stephentissot/NodeNet-SoC-Risc-v/README_NODENET_PLC_COMMANDS.md

# NodeNet PLC Commands

This document describes the NodeNet PLC commands implemented by the firmware for browsing point definitions, browsing point states, managing PLC slots, and deploying PLC programs.

These commands are handled in the NodeNet core and operate on the local point catalog.

Current status: the project is **PLC Ready** with a **V0 basic ISA**. The canonical deployment artifact is a relocatable `objectFileV1` payload uploaded over NodeNet and linked by firmware against the current runtime point catalog.

## Overview

Supported commands:

- `pointDefsReq`
- `pointStatesReq`
- `pointUpsert`
- `pointDelete`
- `plcStatusReq`
- `plcSlotsReq`
- `plcLoadReq`
- `plcBytecodeReq`
- `plcUploadBeginReq`
- `plcUploadStatusReq`
- `plcUploadCommitReq`
- `plcUploadAbortReq`
- `updateProperty` for writable local properties and writable Modbus coil points

PLC upload persistence rules:

- uploads are staged in SDRAM and currently require `autoLoad = true`
- `persistToFlash = true` stores the current slot set in the raw PLC flash package for reboot restore
- `persistToFlash = false` keeps the uploaded artifact volatile

The point identity model is hierarchical:

- `deviceId`
- `feature`
- `pointId`

The optional `path` field used by `pointDefsReq` and `pointStatesReq` is built like this:

```text
deviceId.feature.pointId
```

Examples:

- empty path: browse devices
- `gb9fao5yk4f`: browse one device and its features
- `gb9fao5yk4f.modbus0.eurotherm6100`: browse points under one feature
- `gb9fao5yk4f.modbus0.eurotherm6100.ch1`: browse one exact point

Both browse commands support pagination:

- `offset`: first element to return
- `limit`: maximum number of elements to return
- `count`: number of elements returned in this response
- `total`: total number of matching elements
- `hasMore`: `true` when more elements are available

Transport note:

- when requests are sent from a PC through the NodeNet master bridge, use `from = 255`
- the firmware routes replies back to `request.from`
- `from = 255` is treated as the desktop endpoint and the reply is re-emitted so the PC can receive it through the master
- using `from = 5` or another regular NodeNet address sends the reply to that NodeNet node, not back to the PC link

## plcBytecodeReq

Reads back the linked PLC bytecode currently loaded in one slot.

This command returns the runtime-linked bytecode stored in the slot SDRAM region,
not the original `objectFileV1` source artifact. Symbolic point names are therefore
not preserved in the returned bytes.

### Request

```json
{
  "cmd": "plcBytecodeReq",
  "from": 255,
  "to": 4,
  "slotId": 0,
  "offset": 0,
  "maxBytes": 768
}
```

Fields:

- `slotId`: slot to inspect
- `offset`: byte offset inside the linked slot bytecode
- `maxBytes`: requested maximum chunk size, capped by firmware

### Success response

```json
{
  "cmd": "plcBytecodeRes",
  "ok": true,
  "slotId": 0,
  "offset": 0,
  "count": 96,
  "totalSize": 96,
  "hasMore": false,
  "encoding": "base64",
  "dataBase64": "ECoAEQEA"
}
```

Fields:

- `count`: number of decoded bytecode bytes in this chunk
- `totalSize`: total linked bytecode size for the slot
- `hasMore`: `true` when another chunk must be requested
- `dataBase64`: Base64-encoded linked bytecode bytes

### Failure responses

Possible firmware error values:

- `slotOutOfRange`
- `slotNotLoaded`
- `offsetOutOfRange`

## plcObjectFileReq

Reads back the original `objectFileV1` payload currently retained for one slot.

This command returns the per-slot source artifact snapshot kept in SDRAM after a
successful load. Symbol names, `PARAM`, and `VAR` declarations are preserved and
can be reconstructed by the desktop disassembler.

Persistence note:

- slot `0` can retain a reboot-persistent PLC package in flash
- other slots retain their source snapshot only while the current runtime stays loaded

### Request

```json
{
  "cmd": "plcObjectFileReq",
  "from": 255,
  "to": 4,
  "slotId": 0,
  "offset": 0,
  "maxBytes": 768
}
```

Fields:

- `slotId`: slot to inspect
- `offset`: byte offset inside the retained `objectFileV1` payload
- `maxBytes`: requested maximum chunk size, capped by firmware

### Success response

```json
{
  "cmd": "plcObjectFileRes",
  "ok": true,
  "slotId": 0,
  "offset": 0,
  "count": 164,
  "totalSize": 164,
  "payloadCrc32": 305419896,
  "artifactType": "objectFileV1",
  "hasMore": false,
  "encoding": "base64",
  "dataBase64": "..."
}
```

Fields:

- `count`: number of decoded object bytes in this chunk
- `totalSize`: total retained object size for the slot
- `payloadCrc32`: checksum of the retained object payload
- `artifactType`: always `objectFileV1`
- `hasMore`: `true` when another chunk must be requested
- `dataBase64`: Base64-encoded object bytes

### Failure responses

Possible firmware error values:

- `slotOutOfRange`
- `objectFileUnavailable`
- `encodingFailed`

## pointDefsReq

Requests point definitions from the local catalog.

### Request

```json
{
  "cmd": "pointDefsReq",
  "from": 5,
  "to": 4,
  "path": "",
  "offset": 0,
  "limit": 8
}
```

### Device-level response

With an empty path, or with a `deviceId`, the response kind is `devices`.

```json
{
  "cmd": "pointDefsRes",
  "to": 5,
  "path": "",
  "offset": 0,
  "kind": "devices",
  "count": 1,
  "total": 1,
  "hasMore": false,
  "devices": [
    {
      "deviceId": "gb9fao5yk4f",
      "features": [
        "core",
        "modbus0",
        "modbus0.waveshare8ch",
        "modbus0.eurotherm6100"
      ]
    }
  ]
}
```

### Feature-level response

With a `deviceId.feature` path, the response kind is `points`.

```json
{
  "cmd": "pointDefsRes",
  "to": 5,
  "path": "gb9fao5yk4f.modbus0.eurotherm6100",
  "offset": 0,
  "kind": "points",
  "count": 3,
  "total": 3,
  "hasMore": false,
  "points": [
    {
      "deviceId": "gb9fao5yk4f",
      "feature": "modbus0.eurotherm6100",
      "pointId": "ch1",
      "displayName": "Eurotherm CH1 PV",
      "backend": 1,
      "direction": 0,
      "valueType": 2,
      "refreshMs": 1000,
      "timeoutMs": 3000,
      "stringCapacity": 0,
      "portIndex": 0,
      "slaveAddress": 2,
      "address": 41433,
      "registerCount": 1,
      "table": 3,
      "access": 1
    }
  ]
}
```

## pointStatesReq

Requests live point states from the local catalog.

### Request

```json
{
  "cmd": "pointStatesReq",
  "from": 5,
  "to": 4,
  "path": "gb9fao5yk4f.modbus0.eurotherm6100",
  "offset": 0,
  "limit": 4
}
```

### Point-state response

With a `deviceId.feature` or `deviceId.feature.pointId` path, the response kind is `points` and the returned array is `pointStates`.

`lastUpdateAgeMs` is the elapsed time in milliseconds since the last poll or write attempt for that point.

`lastGoodUpdateAgeMs` is the elapsed time in milliseconds since the last successful poll or write for that point. It stays `0` if the point has never had a good value yet.

```json
{
  "cmd": "pointStatesRes",
  "to": 5,
  "path": "gb9fao5yk4f.modbus0.eurotherm6100",
  "offset": 0,
  "kind": "points",
  "count": 3,
  "total": 3,
  "hasMore": false,
  "pointStates": [
    {
      "deviceId": "gb9fao5yk4f",
      "feature": "modbus0.eurotherm6100",
      "pointId": "ch1",
      "quality": 1,
      "lastUpdateAgeMs": 183,
      "lastGoodUpdateAgeMs": 183,
      "value": 215
    },
    {
      "deviceId": "gb9fao5yk4f",
      "feature": "modbus0.eurotherm6100",
      "pointId": "ch2",
      "quality": 1,
      "lastUpdateAgeMs": 1186,
      "lastGoodUpdateAgeMs": 1186,
      "value": 198
    }
  ]
}
```

### Quality values

`quality` is a numeric `PointQuality` value:

- `0`: `Unknown`
- `1`: `Good`
- `2`: `UncertainInitialValue`
- `3`: `BadNotConnected`
- `4`: `BadNodeMissing`
- `5`: `BadTimeout`
- `6`: `BadProtocolError`
- `7`: `BadConfigError`
- `8`: `BadInvalidValue`
- `9`: `BadWriteRejected`

## pointUpsert

Creates a new point definition or updates an existing one.

### Request

The request payload must contain a `definition` object compatible with the firmware serializer.

```json
{
  "cmd": "pointUpsert",
  "from": 5,
  "to": 4,
  "definition": {
    "deviceId": "gb9fao5yk4f",
    "feature": "modbus0.waveshare8ch",
    "pointId": "output1",
    "displayName": "Output Channel 1",
    "backend": 1,
    "direction": 2,
    "valueType": 0,
    "refreshMs": 1000,
    "timeoutMs": 3000,
    "stringCapacity": 0,
    "portIndex": 0,
    "slaveAddress": 1,
    "address": 0,
    "registerCount": 1,
    "table": 1,
    "access": 3
  }
}
```

### Success response

```json
{
  "cmd": "pointUpsert",
  "ok": true
}
```

### Failure response

```json
{
  "cmd": "pointUpsert",
  "ok": false,
  "error": "invalidDefinition"
}
```

Possible `pointUpsert` errors:

- `invalidDefinition`
- `upsertFailed`

### Numeric enum values used in definition payloads

`backend`:

- `0`: `Local`
- `1`: `Modbus`
- `2`: `NodeNet`

`direction`:

- `0`: `Input`
- `1`: `Output`
- `2`: `InOut`

`valueType`:

- `0`: `Bool`
- `1`: `Uint16`
- `2`: `Int16`
- `3`: `Uint32`
- `4`: `Int32`
- `5`: `Float`
- `6`: `Enum`
- `7`: `String`

For `backend = 1` (`Modbus`), the Modbus-specific fields are:

- `portIndex`
- `slaveAddress`
- `address`
- `registerCount`
- `table`
- `access`

Modbus `table` values:

- `1`: `Coils`
- `2`: `DiscreteInputs`
- `3`: `HoldingRegisters`
- `4`: `InputRegisters`

Modbus `access` values:

- `1`: `Read`
- `2`: `Write`
- `3`: `ReadWrite`

For `backend = 2` (`NodeNet`), use these remote reference fields instead:

- `remoteDeviceId`
- `remoteFeature`
- `remotePointId`

## pointDelete

Deletes one point definition by explicit identity.

### Request

```json
{
  "cmd": "pointDelete",
  "from": 5,
  "to": 4,
  "deviceId": "gb9fao5yk4f",
  "feature": "modbus0.waveshare8ch",
  "pointId": "output8"
}
```

### Success response

```json
{
  "cmd": "pointDelete",
  "ok": true
}
```

### Failure response

```json
{
  "cmd": "pointDelete",
  "ok": false,
  "error": "notFound"
}
```

Possible `pointDelete` errors:

- `missingIdentity`
- `notFound`
- `saveFailed`

## plcStatusReq

Requests detailed PLC runtime status for one slot.

### Request

```json
{
  "cmd": "plcStatusReq",
  "from": 255,
  "to": 4,
  "slotId": 0
}
```

### Response

```json
{
  "cmd": "plcStatusRes",
  "to": 5,
  "ok": true,
  "slotId": 0,
  "state": "running",
  "loaded": true,
  "status": 2,
  "pc": 7,
  "cycleCounter": 885,
  "faultCode": 0,
  "faultInfo": 0,
  "bytecodeBase": 537067584,
  "bytecodeSize": 7,
  "maxInstructionsPerScan": 16,
  "maxScanTimeUs": 5000,
  "source": "local",
  "params": {
    "inputChannel": 1,
    "outputChannel": 1
  },
  "runtimeMapOk": true,
  "inputRuntimeIndex": 0,
  "outputRuntimeIndex": 1,
  "runtimeStoreEpoch": 1,
  "runtimePublishedCount": 21,
  "runtimeHeaderAddr": 537919744
}
```

Possible `state` values:

- `empty`
- `loaded`
- `running`
- `faulted`

## plcSlotsReq

Requests a compact inventory of PLC slots with pagination.

### Request

```json
{
  "cmd": "plcSlotsReq",
  "from": 255,
  "to": 4,
  "offset": 0,
  "limit": 4
}
```

### Response

```json
{
  "cmd": "plcSlotsRes",
  "to": 5,
  "ok": true,
  "offset": 0,
  "count": 4,
  "total": 16,
  "hasMore": true,
  "runtimeStoreEpoch": 1,
  "runtimePublishedCount": 21,
  "slots": [
    {
      "slotId": 0,
      "state": "running",
      "loaded": true,
      "source": "local",
      "cycleCounter": 885,
      "faultCode": 0,
      "bytecodeSize": 7,
      "status": 2
    },
    {
      "slotId": 1,
      "state": "loaded",
      "loaded": true,
      "source": "unknown",
      "cycleCounter": 0,
      "faultCode": 0,
      "bytecodeSize": 6,
      "status": 1
    }
  ]
}
```

## plcLoadReq

Loads the built-in boolean mirror PLC program into a chosen slot.

Documentation note:

- this helper is not the canonical generic deployment format
- the stable PLC deployment contract uses a relocatable `objectFileV1` artifact
  linked by firmware when the slot is loaded or restored
- `plcLoadReq` remains useful as a convenience command for the built-in mirror
  program, but generic host-side deployment should target the object-file flow

### Request

```json
{
  "cmd": "plcLoadReq",
  "from": 255,
  "to": 4,
  "slotId": 0,
  "programType": "mirrorBool",
  "params": {
    "inputChannel": 1,
    "outputChannel": 1
  },
  "persistToFlash": true
}
```

Fields:

- `slotId`: target PLC slot, `0..15`
- `programType`: currently `mirrorBool`
- `params.inputChannel`: Waveshare input channel, `1..8`
- `params.outputChannel`: Waveshare output channel, `1..8`
- `persistToFlash`: optional, persists the slot set into the raw PLC flash package for reboot restore

### Response

```json
{
  "cmd": "plcLoadRes",
  "to": 5,
  "ok": true,
  "slotId": 0,
  "programType": "mirrorBool",
  "params": {
    "inputChannel": 1,
    "outputChannel": 1
  },
  "persistToFlash": true,
  "loadStatus": 0,
  "flashStatus": 0,
  "source": "flash",
  "runtimeMapOk": true,
  "inputRuntimeIndex": 0,
  "outputRuntimeIndex": 1,
  "state": "loaded",
  "cycleCounter": 0,
  "faultCode": 0
}
```

Possible errors:

- `runtimeUnavailable`
- `slotOutOfRange`
- `channelOutOfRange`
- `flashPersistSlot0Only`
- `loadFailed`
- `flashPersistFailed`

## plcUploadBeginReq

Starts a PLC program upload session over NodeNet.

Target V1 scope:

- one upload session at a time
- artifact type must be `objectFileV1`
- upload staging uses SDRAM
- data packets are binary, not JSON
- `persistToFlash` is optional
- `autoLoad` defaults to `true` and is currently required

Current implementation note:

- the firmware upload path now accepts only `objectFileV1`
- point symbols are linked by firmware at commit/load time against the current
  runtime catalog
- `PARAM POINT_ID` declarations are currently bound to full point paths on the
  host side before upload

### Request

```json
{
  "cmd": "plcUploadBeginReq",
  "from": 255,
  "to": 4,
  "slotId": 0,
  "artifactType": "objectFileV1",
  "totalSize": 1536,
  "payloadCrc32": 305419896,
  "persistToFlash": true,
  "autoLoad": true
}
```

### Response

```json
{
  "cmd": "plcUploadBeginRes",
  "to": 255,
  "ok": true,
  "uploadId": 1,
  "acceptedChunkSize": 256,
  "active": true,
  "slotId": 0,
  "artifactType": "objectFileV1",
  "persistToFlash": true,
  "autoLoad": true,
  "totalSize": 1536,
  "bytesReceived": 0,
  "expectedOffset": 0,
  "lastErrorStatus": 0
}
```

Possible errors:

- `runtimeUnavailable`
- `uploadBusy`
- `slotOutOfRange`
- `persistRequired`
- `sizeOutOfRange`
- `unsupportedArtifactType`
- `stagingEraseFailed`

## plcUploadDataReq

After `plcUploadBeginReq`, chunk payloads can be sent with a minimal JSON command.

This path is the recommended one when the desktop talks to the NodeNet master over a serial bridge, because the master relays normal NodeNet JSON messages to the target node.

### Request

```json
{
  "cmd": "plcUploadDataReq",
  "from": 255,
  "to": 4,
  "uploadId": 1,
  "offset": 0,
  "dataHex": "4F424A3101000000..."
}
```

Fields:

- `uploadId`: upload session identifier returned by `plcUploadBeginRes`
- `offset`: byte offset in the staged object file
- `dataHex`: uppercase or lowercase hex payload for one chunk

V1 constraints:

- decoded payload size must be `1..256`
- `offset` must match the next expected offset exactly
- `offset` must be aligned on 256 bytes
- chunks are written as one flash page each
- the last chunk may be shorter than 256 bytes

### Response

Each accepted or rejected chunk generates a JSON acknowledgement.

```json
{
  "cmd": "plcUploadDataRes",
  "to": 255,
  "ok": true,
  "uploadId": 1,
  "offset": 0,
  "bytesReceived": 256,
  "expectedOffset": 256
}
```

Possible chunk errors:

- `noActiveUpload`
- `uploadIdMismatch`
- `offsetMismatch`
- `invalidChunkEncoding`
- `invalidChunkSize`
- `invalidOffset`
- `chunkChecksumMismatch`
- `flashWriteFailed`

## PLC upload binary data packets

As an alternative compatibility path, chunk payloads may still be sent as raw NodeNet binary frames instead of JSON.

Each frame contains a 16-byte header followed by one payload chunk.

### Binary frame header layout

```text
byte  0 : magic = 0xA5
byte  1 : version = 1
byte  2 : reserved low
byte  3 : reserved high
byte  4 : uploadId[7:0]
byte  5 : uploadId[15:8]
byte  6 : uploadId[23:16]
byte  7 : uploadId[31:24]
byte  8 : offset[7:0]
byte  9 : offset[15:8]
byte 10 : offset[23:16]
byte 11 : offset[31:24]
byte 12 : payloadSize[7:0]
byte 13 : payloadSize[15:8]
byte 14 : payloadChecksum[7:0]
byte 15 : payloadChecksum[15:8]
byte 16.. : payload bytes
```

V1 constraints:

- `payloadSize` must be `1..256`
- `offset` must match the next expected offset exactly
- `offset` must be aligned on 256 bytes
- chunks are written as one flash page each
- the last chunk may be shorter than 256 bytes
- `payloadChecksum` is the 16-bit sum of payload bytes

### Data-packet response

Each accepted or rejected binary packet generates a JSON acknowledgement.

```json
{
  "cmd": "plcUploadDataRes",
  "to": 255,
  "ok": true,
  "uploadId": 1,
  "offset": 0,
  "bytesReceived": 256,
  "expectedOffset": 256
}
```

Possible packet errors:

- `uploadIdMismatch`
- `offsetMismatch`
- `invalidChunkSize`
- `invalidOffset`
- `chunkChecksumMismatch`
- `flashWriteFailed`

## plcUploadStatusReq

Returns the current upload-session state.

### Request

```json
{
  "cmd": "plcUploadStatusReq",
  "from": 255,
  "to": 4
}
```

### Response

```json
{
  "cmd": "plcUploadStatusRes",
  "to": 255,
  "ok": true,
  "active": true,
  "slotId": 0,
  "uploadId": 1,
  "artifactType": "objectFileV1",
  "persistToFlash": true,
  "autoLoad": true,
  "totalSize": 1536,
  "bytesReceived": 512,
  "expectedOffset": 512,
  "lastErrorStatus": 0
}
```

## plcUploadCommitReq

Finalizes the upload, verifies the whole payload checksum, resolves point
symbols against the current runtime catalog, and loads the linked slot image
when `autoLoad` is enabled.

On the stable object-file path, commit/load performs the following steps:

1. parse the uploaded PLC object file
2. read every stored point symbol path from the object file
3. resolve every `CONST POINT_ID` and `PARAM POINT_ID` symbol
4. patch relocations to runtime indices
5. write the linked image into SDRAM and arm the target slot

### Request

```json
{
  "cmd": "plcUploadCommitReq",
  "from": 255,
  "to": 4,
  "uploadId": 1
}
```

### Response

```json
{
  "cmd": "plcUploadCommitRes",
  "to": 255,
  "ok": true,
  "slotId": 0,
  "loadStatus": 0,
  "active": true,
  "uploadId": 1,
  "bytesReceived": 1536,
  "expectedOffset": 1536
}
```

Possible errors:

- `runtimeUnavailable`
- `noActiveUpload`
- `uploadIdMismatch`
- `uploadIncomplete`
- `payloadChecksumMismatch`
- `parseFailed`
- `pointResolveFailed`
- `loadFailed`

When `loadFailed` is returned, `loadStatus` contains the `PlcSlotLoadStatusV1` numeric value.

## plcUploadAbortReq

Cancels the active upload session.

### Request

```json
{
  "cmd": "plcUploadAbortReq",
  "from": 255,
  "to": 4,
  "uploadId": 1
}
```

### Response

```json
{
  "cmd": "plcUploadAbortRes",
  "to": 255,
  "ok": true
}
```

Possible errors:

- `noActiveUpload`
- `uploadIdMismatch`

## PLC point model

The firmware also exposes PLC state and control through normal point definitions.

Available local features now include:

- `plc`
- `plc.slot0` to `plc.slot15`

The global `plc` feature exposes read-only points such as:

- `slotCount`
- `activeSlotCount`
- `faultedSlotCount`
- `runtimeStoreEpoch`
- `runtimePublishedCount`

Each `plc.slotN` feature exposes read-only points such as:

- `loaded`
- `state`
- `runEnabled`
- `status`
- `cycleCounter`
- `faultCode`
- `faultInfo`
- `bytecodeSize`
- `source`
- `programType`
- `paramsSummary`
- `inputChannel`
- `outputChannel`
- `runtimeMapOk`

Each `plc.slotN` feature also exposes command-like boolean points:

- `start`
- `stop`
- `reset`
- `clearFault`

Current slot state values are:

- `empty`
- `loaded`
- `running`
- `stopped`
- `faulted`

## updateProperty for point writes

The existing `updateProperty` command can also be used to write some runtime PLC values.

Two write categories are currently supported:

- local NodeNetCore properties such as `instrumentName`, `master`, and `modbus0.*`
- Modbus coil points addressed by their full point path
- PLC slot control points addressed by their full point path

For Modbus point writes, the current implementation is intentionally narrow:

- backend must be `Modbus`
- table must be `Coils`
- value type must be `Bool`
- access must be `Write` or `ReadWrite`

For local Modbus port configuration, `updateProperty` also accepts writable properties under `modbus0.*`, including `modbus0.speed`, `modbus0.timeout`, `modbus0.retries`, `modbus0.interframeCharsQ1`, and `modbus0.maxGap`.

That matches Waveshare outputs such as `output1`.

For PLC control-point writes, the current implementation supports only local points under `plc.slotN`:

- `start`
- `stop`
- `reset`
- `clearFault`

These points behave like impulse commands:

- write `true` to request the action
- the runtime point state is republished back to `false`

`start` and `stop` toggle the slot paused state.

`reset` clears runtime counters and faults and rewinds the slot PC to its entry offset.

`clearFault` only clears the current fault state.

### Example: set Waveshare output1 ON

```json
{
  "cmd": "updateProperty",
  "from": 5,
  "to": 4,
  "propertyName": "gb9fao5yk4f.modbus0.waveshare8ch.output1",
  "value": true
}
```

### Example: set Waveshare output1 OFF

```json
{
  "cmd": "updateProperty",
  "from": 5,
  "to": 4,
  "propertyName": "gb9fao5yk4f.modbus0.waveshare8ch.output1",
  "value": false
}
```

When the Modbus write succeeds, the point state is updated locally to the commanded boolean value.

### Example: change Modbus0 speed

```json
{
  "cmd": "updateProperty",
  "from": 5,
  "to": 4,
  "propertyName": "modbus0.speed",
  "value": 9600
}
```

### Example: change Modbus0 batch max gap

`modbus0.maxGap` controls how many unneeded addressed items the firmware may span while merging adjacent Modbus reads into one batch. The default is `6`.

```json
{
  "cmd": "updateProperty",
  "from": 5,
  "to": 4,
  "propertyName": "modbus0.maxGap",
  "value": 6
}
```

### Example: stop PLC slot0

```json
{
  "cmd": "updateProperty",
  "from": 255,
  "to": 4,
  "propertyName": "gb9fao5yk4f.plc.slot0.stop",
  "value": true
}
```

### Example: restart PLC slot0

```json
{
  "cmd": "updateProperty",
  "from": 255,
  "to": 4,
  "propertyName": "gb9fao5yk4f.plc.slot0.start",
  "value": true
}
```

### Example: clear a PLC slot0 fault

```json
{
  "cmd": "updateProperty",
  "from": 255,
  "to": 4,
  "propertyName": "gb9fao5yk4f.plc.slot0.clearFault",
  "value": true
}
```

## Notes

- `pointDefsReq` returns definitions in the `points` array.
- `pointStatesReq` returns runtime values in the `pointStates` array.
- `pointUpsert` persists the updated point catalog.
- `pointDelete` removes the point from the catalog and then persists the catalog.
- Responses are size-limited by the NodeNet payload maximum, so large result sets may be split across multiple pages.
