stephentissot/NodeNet-SoC-Risc-v/src/firmware/include/plc_runtime_abi.h

#ifndef PLC_RUNTIME_ABI_H
#define PLC_RUNTIME_ABI_H

#include <cstddef>
#include <cstdint>
#include <cstring>

#include "PointCatalog.h"
#include "sdram.h"

static constexpr uint32_t kPlcRuntimeAbiV1Magic = 0x31564D50u;
static constexpr uint16_t kPlcRuntimeAbiV1Version = 1u;
static constexpr uint32_t kPlcRuntimeHeaderAddr = SDRAM_BASE + 0x00100000u;
static constexpr uint32_t kPlcRuntimeDescriptorBase = SDRAM_BASE + 0x00100100u;
static constexpr uint32_t kPlcRuntimeDescriptorWindowSize = 0x00010000u;
static constexpr uint32_t kPlcSharedPointStateBase = SDRAM_POINT_STATE_BASE;
static constexpr uint32_t kPlcSharedPointStateStride = static_cast<uint32_t>(sizeof(PointState));
static constexpr uint32_t kPlcSharedPointStateValueOffset = static_cast<uint32_t>(offsetof(PointState, value));
static constexpr uint32_t kPlcSharedPointStateQualityOffset = static_cast<uint32_t>(offsetof(PointState, quality));
static constexpr uint32_t kPlcSharedPointStateLastUpdateOffset = static_cast<uint32_t>(offsetof(PointState, last_update_ms));
static constexpr uint32_t kPlcSharedPointStateLastGoodUpdateOffset = static_cast<uint32_t>(offsetof(PointState, last_good_update_ms));

enum PlcRuntimeValueTypeV1 : uint8_t {
    kPlcRuntimeTypeInvalid = 0u,
    kPlcRuntimeTypeBool = 1u,
    kPlcRuntimeTypeUint16 = 2u,
    kPlcRuntimeTypeInt16 = 3u,
    kPlcRuntimeTypeUint32 = 4u,
    kPlcRuntimeTypeInt32 = 5u,
    kPlcRuntimeTypeFloat32 = 6u,
};

enum PlcRuntimeDescriptorFlagsV1 : uint8_t {
    kPlcRuntimeFlagReadable = 1u << 0,
    kPlcRuntimeFlagWritable = 1u << 1,
    kPlcRuntimeFlagInput = 1u << 2,
    kPlcRuntimeFlagOutput = 1u << 3,
    kPlcRuntimeFlagInternal = 1u << 4,
    kPlcRuntimeFlagFloat = 1u << 5,
    kPlcRuntimeFlagSharedPointState = 1u << 6,
};

enum PlcRuntimeLastWriterV1 : uint32_t {
    kPlcRuntimeWriterUnknown = 0u,
    kPlcRuntimeWriterCpu = 1u,
    kPlcRuntimeWriterPlcVm = 2u,
    kPlcRuntimeWriterFieldbus = 3u,
    kPlcRuntimeWriterNodeNet = 4u,
};

enum PlcRuntimeLinkAccessV1 : uint8_t {
    kPlcRuntimeLinkRead = 0u,
    kPlcRuntimeLinkWrite = 1u,
    kPlcRuntimeLinkReadWrite = 2u,
};

enum PlcRuntimeLinkStatusV1 : uint8_t {
    kPlcRuntimeLinkResolved = 0u,
    kPlcRuntimeLinkNotFound = 1u,
    kPlcRuntimeLinkUnsupportedPointType = 2u,
    kPlcRuntimeLinkTypeMismatch = 3u,
    kPlcRuntimeLinkAccessDenied = 4u,
};

#pragma pack(push, 1)
struct PlcPointDescriptorV1 {
    uint16_t point_state_index;
    uint8_t value_type;
    uint8_t flags;
    uint32_t point_state_value_offset;
    uint32_t point_state_quality_offset;
    uint32_t reserved0;
    uint32_t reserved1;
};

struct PlcRuntimeHeaderV1 {
    uint32_t magic;
    uint16_t version;
    uint16_t flags;
    uint32_t descriptor_count;
    uint32_t descriptor_base;
    uint32_t point_state_base;
    uint32_t point_state_stride;
    uint32_t store_epoch;
};
#pragma pack(pop)
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
